DavidMiles1925/printer_camera/profiles/CREALITY_LD-002H_SULNU_Clear_Blue_profile.cfg

__resin:SUNLU Clear Blue
actualPrintingTimeHour:
actualPrintingTimeMinute:
actualPrintingTimeSecond:
antiAliasLevel:8
bAntiAliasLevelEditable:0
bAntiAliasing:1
bBottomInnerOutterCircleOffsetEnable:0
bBuildAreaOffsetEnable:0
bDisplayCorrectEnable:0
bImageBlur:0
bImageBlurPixelEditable:1
bImageMask:0
bInnerOutterCircleOffsetEnable:0
bLockXYSizeRatio:1
bPrintTimeCompensationEnable:
bShrinkageXYRatio:0
bSurfaceRoughEditable:0
bVisibleShrinkageXYRatio:1
bottomEdgeExposureMM:0
bottomEdgeExposureTimeS:4
bottomExposureTimeStrategy:0
bottomInnerCircleOffset:0
bottomLayerCount:8
bottomLayerDropHeight2:
bottomLayerDropSpeed:150
bottomLayerDropSpeed2:
bottomLayerExposureTime:12
bottomLayerLiftHeight:5
bottomLayerLiftHeight2:0
bottomLayerLiftSpeed:50
bottomLayerLiftSpeed2:0
bottomLightIntensityPWM:255
bottomLightOffTime:0
bottomLightOffTimeVisible:1
bottomOutterCircleOffset:0
bottomRestTimeAfterLift:0
bottomRestTimeAfterRetract:0
bottomRestTimeBeforeLift:0
buildAreaOffsetBottom:0
buildAreaOffsetLeft:0
buildAreaOffsetRight:0
buildAreaOffsetTop:0
circleParityDifference:0
currProfile:SULNU Clear Blue
displayCorrectLeftBottomX:0
displayCorrectLeftBottomY:0
displayCorrectLeftTopX:0
displayCorrectLeftTopY:0
displayCorrectRightBottomX:0
displayCorrectRightBottomY:0
displayCorrectRightTopX:0
displayCorrectRightTopY:0
edgeExposureMM:0
edgeExposureTimeS:4
endGcode:"M106 S0;\nG1 Z{machine_height} F25;\nM18;\n"
fillDensity:10
fillPattern:None
imageBlurPixel:2
imageMaskFile:
innerCircleOffset:0
isHALOT:0
isSupportTSMC:0
layerGcode:"M6054 {image};show Image\nG0 Z{rise_pos} F{rise_speed};\nG0 Z{fall_pos} F{fall_speed};\nG4 P{light_delay};\nM106 S{light_pwm};light on\nG4 P{exposure_time};\nM106 S0; light off\n"
layerHeight:0.05
layerPrintTime:
lightOffTime:2
machineDepth:130.56
machineHeight:160
machineType:CREALITY LD-002H
machineWidth:82.62
maskGrayScaleUnit:4
maxGreyLevel:255
minGreyLevel:0
normalExposureTime:2.5
normalLayerDropHeight2:0
normalLayerDropSpeed:150
normalLayerDropSpeed2:0
normalLayerLiftHeight:5
normalLayerLiftHeight2:0
normalLayerLiftSpeed:50
normalLayerLiftSpeed2:0
normalLightIntensityPWM:255
normalRestTimeAfterLift:0
normalRestTimeAfterRetract:0
normalRestTimeBeforeLift:0
outterCircleOffset:0
printWaitMode:0
printingLayer:1
projectType:LCD_mirror
resinDensity:1.1399
resinPrice:19.84
resinUnit:$/L
resolutionX:1620
resolutionY:2560
shellThickness:1.2
sliceExportPart:0
softwareForecastTimeHour:
softwareForecastTimeMinute:
softwareForecastTimeSecond:
startGcode:"G21;\nG90;\nM106 S0;\nG28 Z0;\n"
surfaceRoughLevel:1
transitionLayerCount:0
transitionLayerType:0
waitModeChangedVisible:1
xShrinkageCompensation:100
yShrinkageCompensation:100
zShrinkageCompensation:100
zSlowUpDistance:0
@@SULNU Clear Blue@@__resin:SUNLU Clear Blue
@@SULNU Clear Blue@@actualPrintingTimeHour:
@@SULNU Clear Blue@@actualPrintingTimeMinute:
@@SULNU Clear Blue@@actualPrintingTimeSecond:
@@SULNU Clear Blue@@antiAliasLevel:8
@@SULNU Clear Blue@@bAntiAliasLevelEditable:0
@@SULNU Clear Blue@@bAntiAliasing:1
@@SULNU Clear Blue@@bBottomInnerOutterCircleOffsetEnable:0
@@SULNU Clear Blue@@bBuildAreaOffsetEnable:0
@@SULNU Clear Blue@@bDisplayCorrectEnable:0
@@SULNU Clear Blue@@bImageBlur:0
@@SULNU Clear Blue@@bImageBlurPixelEditable:1
@@SULNU Clear Blue@@bImageMask:0
@@SULNU Clear Blue@@bInnerOutterCircleOffsetEnable:0
@@SULNU Clear Blue@@bLockXYSizeRatio:1
@@SULNU Clear Blue@@bPrintTimeCompensationEnable:
@@SULNU Clear Blue@@bShrinkageXYRatio:0
@@SULNU Clear Blue@@bSurfaceRoughEditable:0
@@SULNU Clear Blue@@bVisibleShrinkageXYRatio:1
@@SULNU Clear Blue@@bottomEdgeExposureMM:0
@@SULNU Clear Blue@@bottomEdgeExposureTimeS:4
@@SULNU Clear Blue@@bottomExposureTimeStrategy:0
@@SULNU Clear Blue@@bottomInnerCircleOffset:0
@@SULNU Clear Blue@@bottomLayerCount:8
@@SULNU Clear Blue@@bottomLayerDropHeight2:
@@SULNU Clear Blue@@bottomLayerDropSpeed:150
@@SULNU Clear Blue@@bottomLayerDropSpeed2:
@@SULNU Clear Blue@@bottomLayerExposureTime:12
@@SULNU Clear Blue@@bottomLayerLiftHeight:5
@@SULNU Clear Blue@@bottomLayerLiftHeight2:0
@@SULNU Clear Blue@@bottomLayerLiftSpeed:50
@@SULNU Clear Blue@@bottomLayerLiftSpeed2:0
@@SULNU Clear Blue@@bottomLightIntensityPWM:255
@@SULNU Clear Blue@@bottomLightOffTime:0
@@SULNU Clear Blue@@bottomLightOffTimeVisible:1
@@SULNU Clear Blue@@bottomOutterCircleOffset:0
@@SULNU Clear Blue@@bottomRestTimeAfterLift:0
@@SULNU Clear Blue@@bottomRestTimeAfterRetract:0
@@SULNU Clear Blue@@bottomRestTimeBeforeLift:0
@@SULNU Clear Blue@@buildAreaOffsetBottom:0
@@SULNU Clear Blue@@buildAreaOffsetLeft:0
@@SULNU Clear Blue@@buildAreaOffsetRight:0
@@SULNU Clear Blue@@buildAreaOffsetTop:0
@@SULNU Clear Blue@@circleParityDifference:0
@@SULNU Clear Blue@@currProfile:ANYCUBIC Gray
@@SULNU Clear Blue@@currProfileName:SULNU Clear Blue
@@SULNU Clear Blue@@displayCorrectLeftBottomX:0
@@SULNU Clear Blue@@displayCorrectLeftBottomY:0
@@SULNU Clear Blue@@displayCorrectLeftTopX:0
@@SULNU Clear Blue@@displayCorrectLeftTopY:0
@@SULNU Clear Blue@@displayCorrectRightBottomX:0
@@SULNU Clear Blue@@displayCorrectRightBottomY:0
@@SULNU Clear Blue@@displayCorrectRightTopX:0
@@SULNU Clear Blue@@displayCorrectRightTopY:0
@@SULNU Clear Blue@@edgeExposureMM:0
@@SULNU Clear Blue@@edgeExposureTimeS:4
@@SULNU Clear Blue@@endGcode:M106 S0;\nG1 Z{machine_height} F25;\nM18;\n
@@SULNU Clear Blue@@fillDensity:10
@@SULNU Clear Blue@@fillPattern:None
@@SULNU Clear Blue@@imageBlurPixel:2
@@SULNU Clear Blue@@imageMaskFile:
@@SULNU Clear Blue@@innerCircleOffset:0
@@SULNU Clear Blue@@isHALOT:0
@@SULNU Clear Blue@@isSupportTSMC:0
@@SULNU Clear Blue@@layerGcode:M6054 {image};show Image\nG0 Z{rise_pos} F{rise_speed};\nG0 Z{fall_pos} F{fall_speed};\nG4 P{light_delay};\nM106 S{light_pwm};light on\nG4 P{exposure_time};\nM106 S0; light off\n
@@SULNU Clear Blue@@layerHeight:0.05
@@SULNU Clear Blue@@layerPrintTime:
@@SULNU Clear Blue@@lightOffTime:2
@@SULNU Clear Blue@@machineDepth:130.56
@@SULNU Clear Blue@@machineHeight:160
@@SULNU Clear Blue@@machineType:CREALITY LD-002H
@@SULNU Clear Blue@@machineWidth:82.62
@@SULNU Clear Blue@@maskGrayScaleUnit:4
@@SULNU Clear Blue@@maxGreyLevel:255
@@SULNU Clear Blue@@minGreyLevel:0
@@SULNU Clear Blue@@normalExposureTime:2.5
@@SULNU Clear Blue@@normalLayerDropHeight2:0
@@SULNU Clear Blue@@normalLayerDropSpeed:150
@@SULNU Clear Blue@@normalLayerDropSpeed2:0
@@SULNU Clear Blue@@normalLayerLiftHeight:5
@@SULNU Clear Blue@@normalLayerLiftHeight2:0
@@SULNU Clear Blue@@normalLayerLiftSpeed:50
@@SULNU Clear Blue@@normalLayerLiftSpeed2:0
@@SULNU Clear Blue@@normalLightIntensityPWM:255
@@SULNU Clear Blue@@normalRestTimeAfterLift:0
@@SULNU Clear Blue@@normalRestTimeAfterRetract:0
@@SULNU Clear Blue@@normalRestTimeBeforeLift:0
@@SULNU Clear Blue@@outterCircleOffset:0
@@SULNU Clear Blue@@printWaitMode:0
@@SULNU Clear Blue@@printingLayer:1
@@SULNU Clear Blue@@projectType:LCD_mirror
@@SULNU Clear Blue@@resinDensity:1.1399
@@SULNU Clear Blue@@resinPrice:19.84
@@SULNU Clear Blue@@resinUnit:$/L
@@SULNU Clear Blue@@resolutionX:1620
@@SULNU Clear Blue@@resolutionY:2560
@@SULNU Clear Blue@@shellThickness:1.2
@@SULNU Clear Blue@@sliceExportPart:0
@@SULNU Clear Blue@@softwareForecastTimeHour:
@@SULNU Clear Blue@@softwareForecastTimeMinute:
@@SULNU Clear Blue@@softwareForecastTimeSecond:
@@SULNU Clear Blue@@startGcode:G21;\nG90;\nM106 S0;\nG28 Z0;\n
@@SULNU Clear Blue@@surfaceRoughLevel:1
@@SULNU Clear Blue@@transitionLayerCount:0
@@SULNU Clear Blue@@transitionLayerType:0
@@SULNU Clear Blue@@waitModeChangedVisible:1
@@SULNU Clear Blue@@xShrinkageCompensation:100
@@SULNU Clear Blue@@yShrinkageCompensation:100
@@SULNU Clear Blue@@zShrinkageCompensation:100
@@SULNU Clear Blue@@zSlowUpDistance:0
