DavidMiles1925/printer_camera/temp.py

import os
import glob
import time

from logger import write_to_log
from config import TEMP_LOG_TIME
 
os.system('modprobe w1-gpio')
os.system('modprobe w1-therm')
 
base_dir = '/sys/bus/w1/devices/'
device_folder = glob.glob(base_dir + '28*')[0]
device_file = device_folder + '/w1_slave'

def construct_temp_string():
    temps = read_temp()
    temp_string = f"C:  {round(temps[0], 2)}    F:  {round(temps[1], 2)}"
    return temp_string
 
def read_temp_raw():
    f = open(device_file, 'r')
    lines = f.readlines()
    f.close()
    return lines
 
def read_temp():
    lines = read_temp_raw()
    while lines[0].strip()[-3:] != 'YES':
        time.sleep(0.2)
        lines = read_temp_raw()
    equals_pos = lines[1].find('t=')
    if equals_pos != -1:
        temp_string = lines[1][equals_pos+2:]
        temp_c = float(temp_string) / 1000.0
        temp_f = temp_c * 9.0 / 5.0 + 32.0
        return temp_c, temp_f


if __name__ == "__main__":
    try:
        while True:
            temp_string = construct_temp_string()
            print(temp_string)
            write_to_log(temp_string, "Tempertaure_Log")
            time.sleep(TEMP_LOG_TIME)

    except KeyboardInterrupt as e:
        print("Program was stopped with Ctrl+C")

    except Exception as e:
        print(e)
